osok/BRAT/BRAT/Config-Example.h

/**
 * This file should not be checked into source control
 * It contains the SSID and Password
 *
 * IMPORTANT  : Rename this file to Config.h
 *
 * Change the SSID and password to reflect what you want to use.
 */

#ifndef CONFIG_H
#define CONFIG_H

/* Set these to your desired credentials. */
const char *ssid = "iPhone";
const char *password = "PutYourPassPhraseHere";


#endif
